andremdaraujo/EMBARCADOS-CURSO-PCB/HARDWARE/KICAD/FABRICATION/GERBER (ReV. 02)/PDF/EMBARCADOS - CURSO PCB-F_Courtyard.pdf

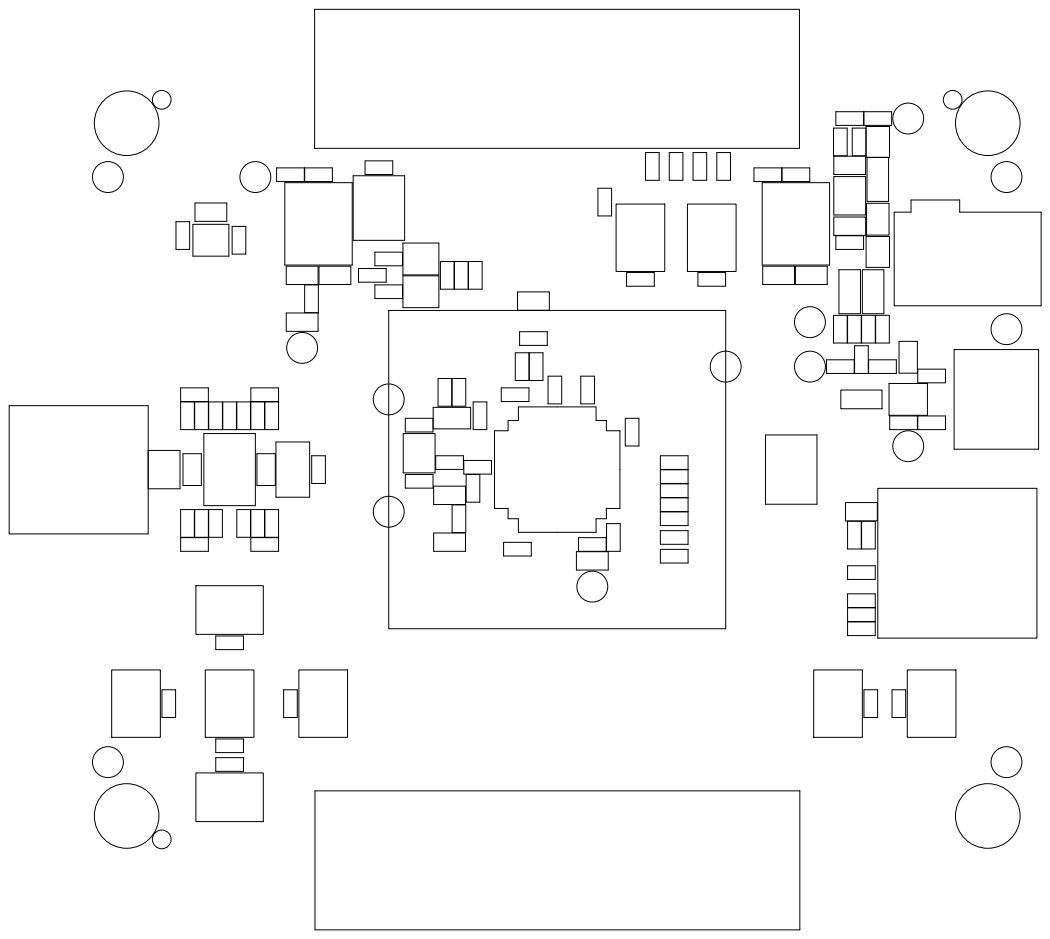
[picture p33: page 1]

Id: 1/1 Title: EMBARCADOS - CURSO PCB
