andremdaraujo/EMBARCADOS-CURSO-PCB/HARDWARE/KICAD/FABRICATION/GERBER (ReV. 02)/PDF/EMBARCADOS - CURSO PCB-F_Mask.pdf

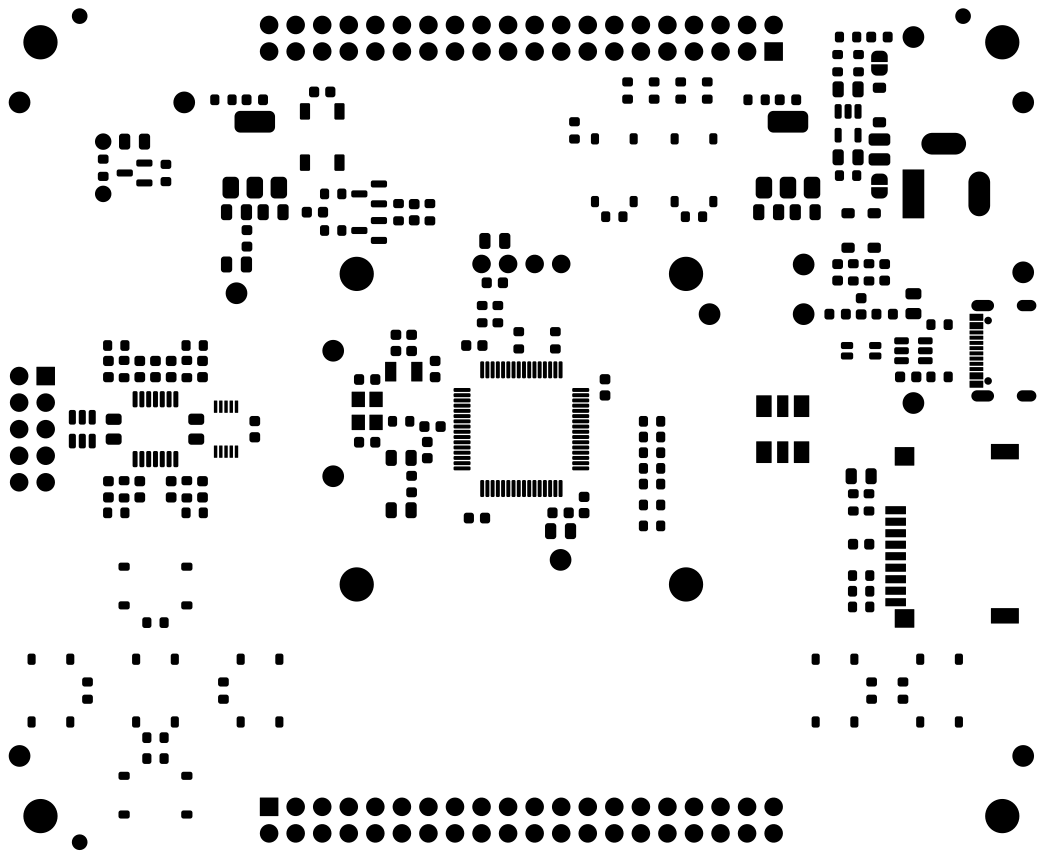
[picture p35: page 1]

Id: 1/1 Title: EMBARCADOS - CURSO PCB
