andremdaraujo/EMBARCADOS-CURSO-PCB/HARDWARE/KICAD/FABRICATION/GERBER (ReV. 02)/PDF/EMBARCADOS - CURSO PCB-F_Silkscreen.pdf

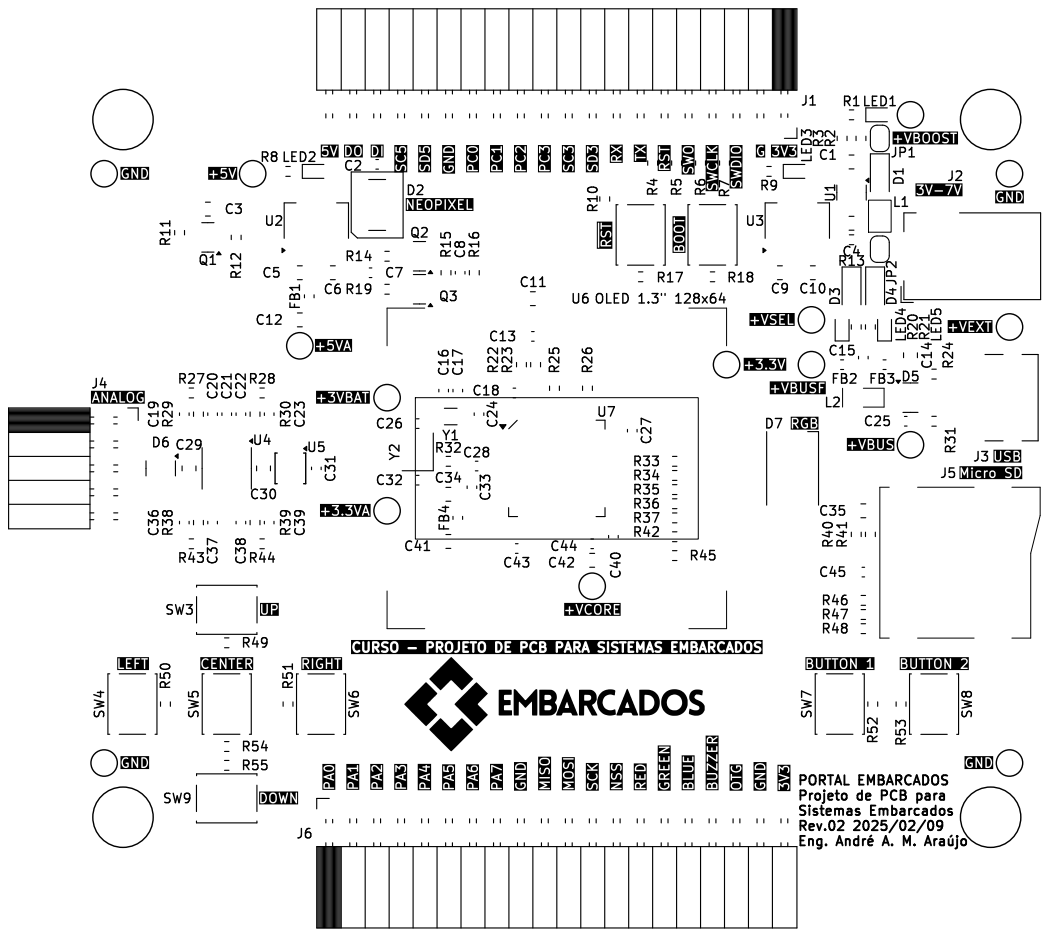
[picture p37: page 1]

Projeto de PCB para Sistemas Embarcados Rev.02 2025/02/09 Eng. þÿAndré A. M. þÿAraújo U6 OLED 1.3" 128x64

Id: 1/1 Title: EMBARCADOS - CURSO PCB
