andremdaraujo/EMBARCADOS-CURSO-PCB/HARDWARE/KICAD/FABRICATION/GERBER (ReV. 02)/PDF/EMBARCADOS - CURSO PCB-L1 - TOP (SIG-PWR).pdf

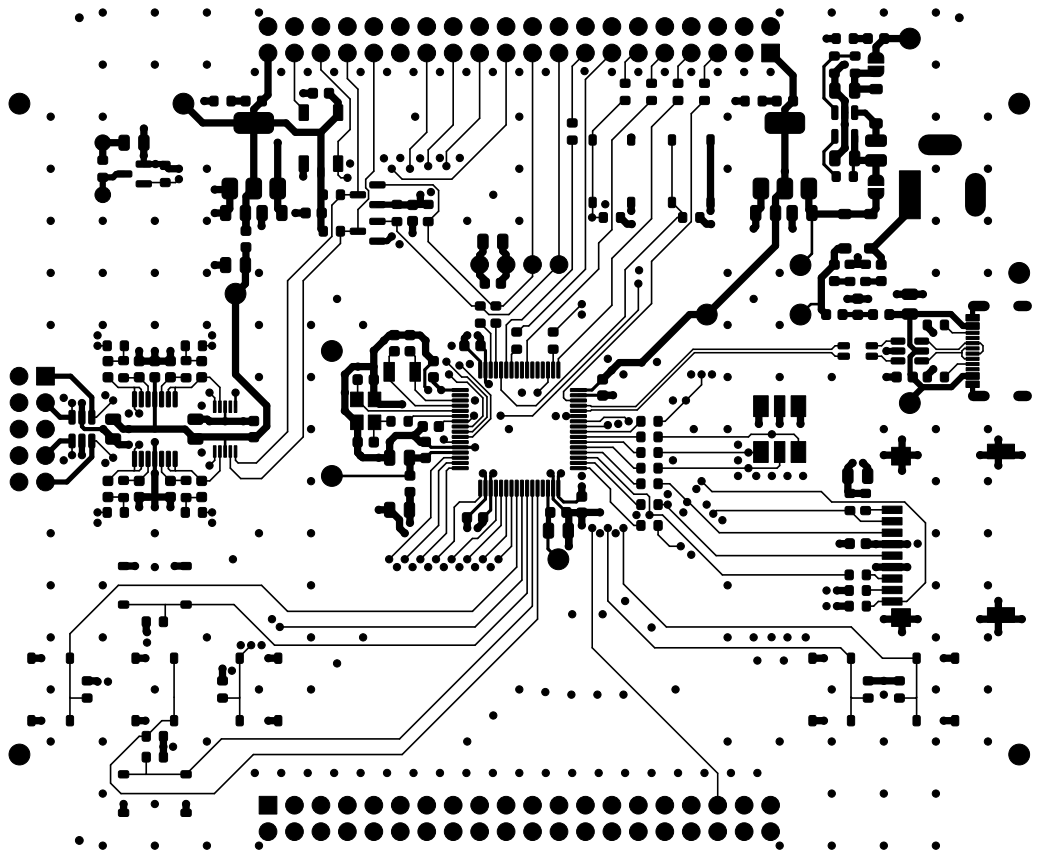
[picture p38: page 1]

Id: 1/1 Title: EMBARCADOS - CURSO PCB
