andremdaraujo/EMBARCADOS-CURSO-PCB/HARDWARE/KICAD/FABRICATION/GERBER (ReV. 02)/PDF/EMBARCADOS - CURSO PCB-L2 - GND.pdf

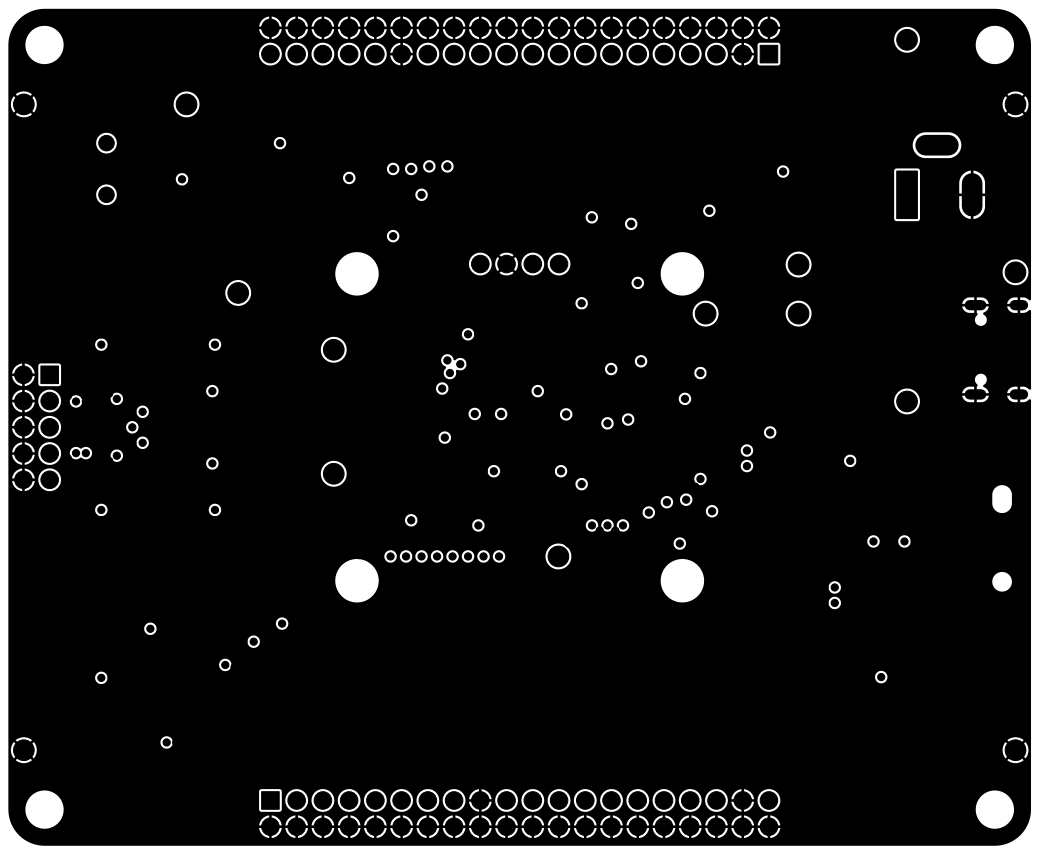
[picture p39: page 1]

Id: 1/1 Title: EMBARCADOS - CURSO PCB
