andremdaraujo/EMBARCADOS-CURSO-PCB/HARDWARE/KICAD/FABRICATION/GERBER (ReV. 02)/PDF/EMBARCADOS - CURSO PCB-L3 - GND.pdf

Id: 1/1 Title: EMBARCADOS - CURSO PCB
