andremdaraujo/EMBARCADOS-CURSO-PCB/HARDWARE/KICAD/FABRICATION/GERBER (ReV. 02)/PDF/EMBARCADOS - CURSO PCB-L4 - BOTTOM (SIG-PWR).pdf

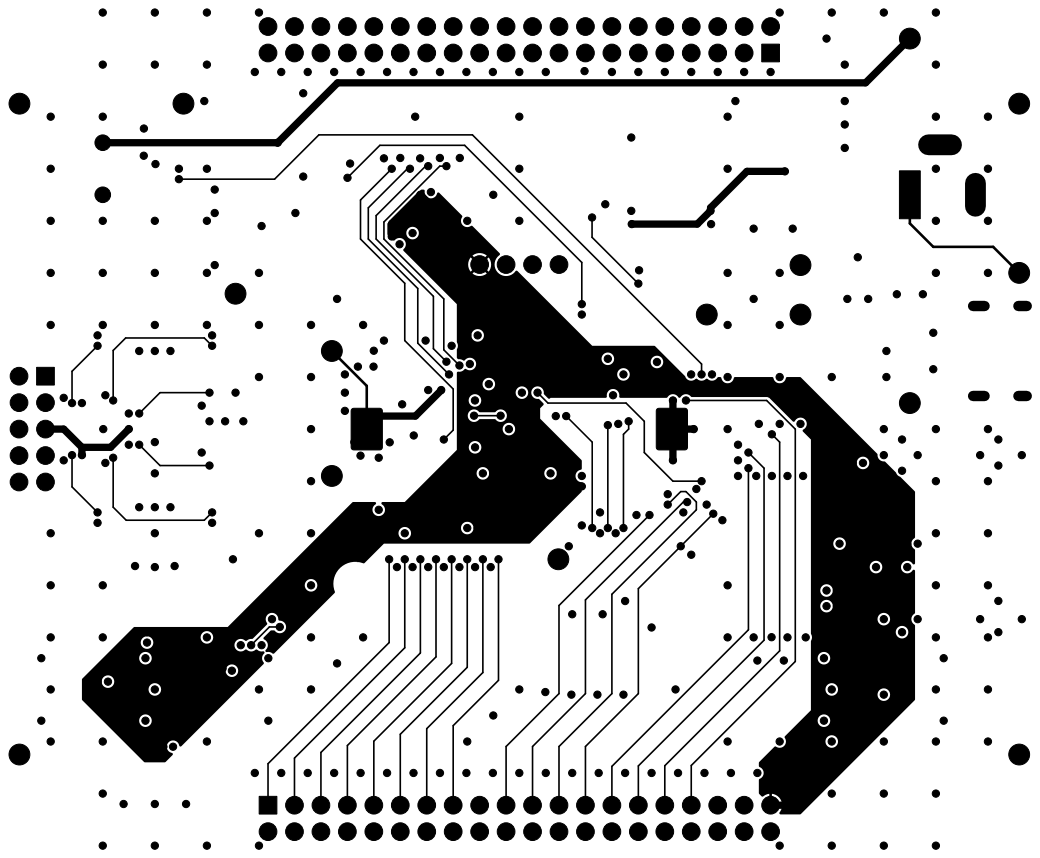
[picture p40: page 1]

Id: 1/1 Title: EMBARCADOS - CURSO PCB
