andremdaraujo/EMBARCADOS-CURSO-PCB/HARDWARE/KICAD/FABRICATION/GERBER (ReV. 02)/PDF/EMBARCADOS - CURSO PCB-User_Comments.pdf

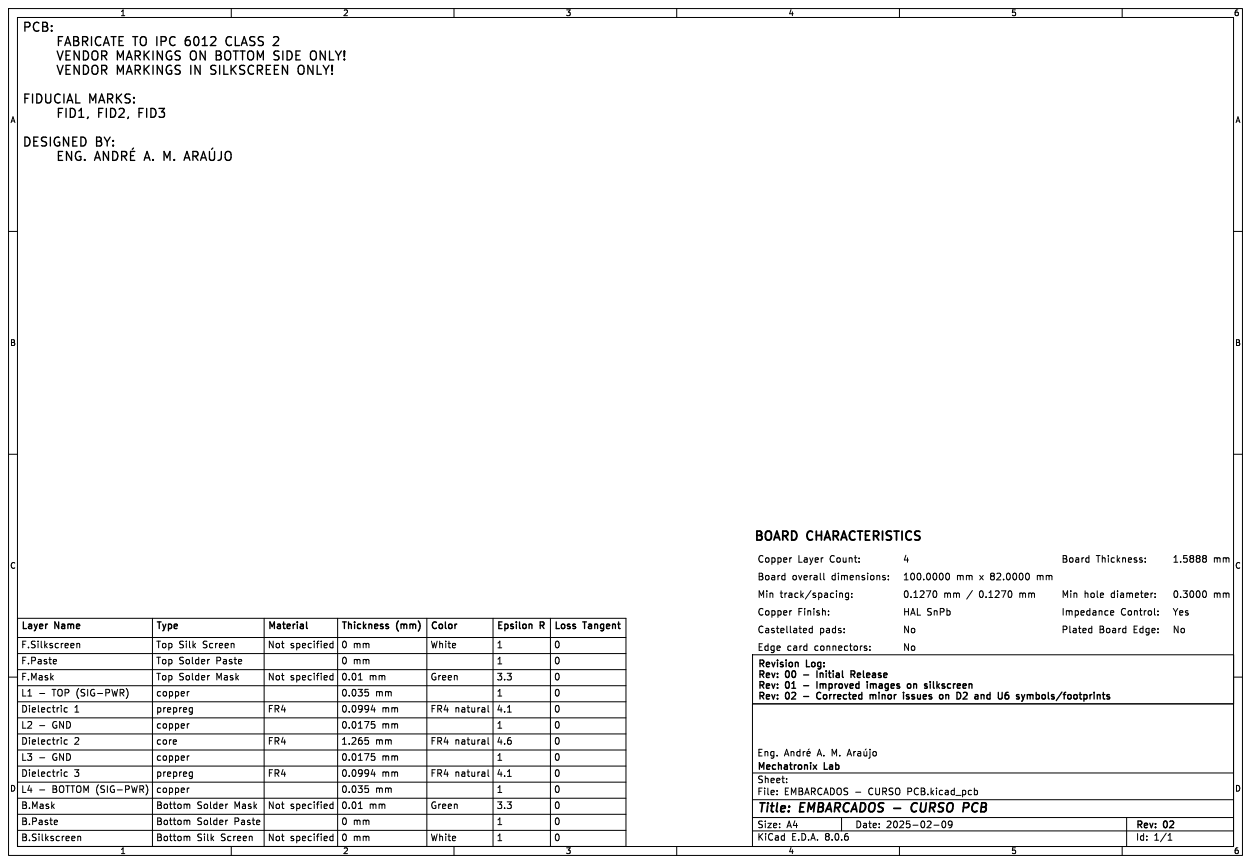
[picture p42: page 1]

Layer Name | | Top Silk Screen | FR4 | 0 mm | 0

Type

L2 - GND | | | | 1 | 0
2 | | 0.0175 mm | | 3.3 1 | 0 Dielectric

copper core | 1.265 mm | FR4 natural 0.0175 mm | | 0

prepreg | | | 4.1 | 0

Id: 1/1 Title: EMBARCADOS - CURSO PCB

0 mm
